BenjaminSoelberg/elektronika-1/src/driverlib/MSP430FR2xx_4xx/driverlib.h

#include "inc/hw_memmap.h"

#include "rom_driverlib.h"
#include "rom_map_driverlib.h"

#include "lcd_e.h"
#include "eusci_b_i2c.h"
#include "ecomp.h"
#include "cs.h"
#include "sac.h"
#include "timer_b.h"
#include "framctl.h"
#include "eusci_a_spi.h"
#include "eusci_a_uart.h"
#include "tia.h"
#include "tlv.h"
#include "timer_a.h"
#include "pmm.h"
#include "sysctl.h"
#include "sfr.h"
#include "mpy32.h"
#include "wdt_a.h"
#include "icc.h"
#include "rom_map_driverlib.h"
#include "gpio.h"
#include "eusci_b_spi.h"
#include "rom_driverlib.h"
#include "adc.h"
#include "crc.h"
#include "rtc.h"
